jandejongh/pa3gyf-gpsdocxo/doc/dcim/2016-12-09 10.36.47-1.jpg

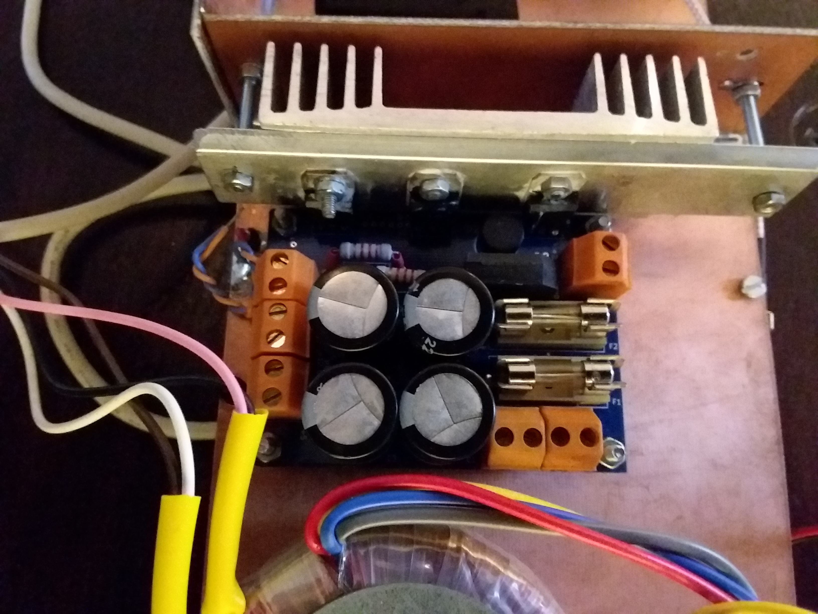
doc/dcim/2016-12-09 10.36.47-1.jpg
