jandejongh/pa3gyf-gpsdocxo/doc/dcim/2016-12-09 10.37.08.jpg

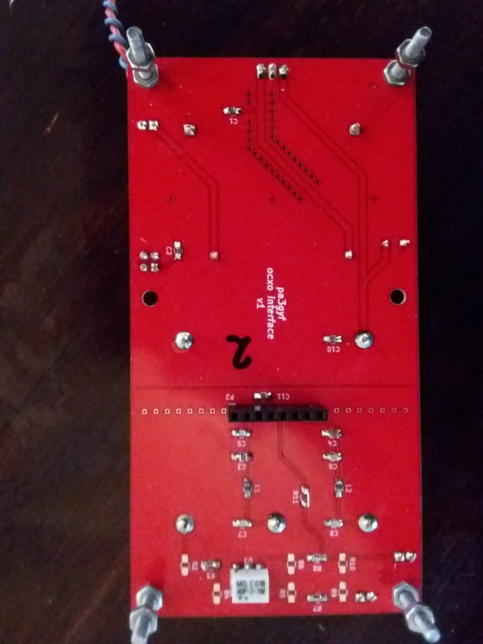
doc/dcim/2016-12-09 10.37.08.jpg
