jandejongh/pa3gyf-gpsdocxo/doc/dcim/2019-09-18 21.45.28.jpg

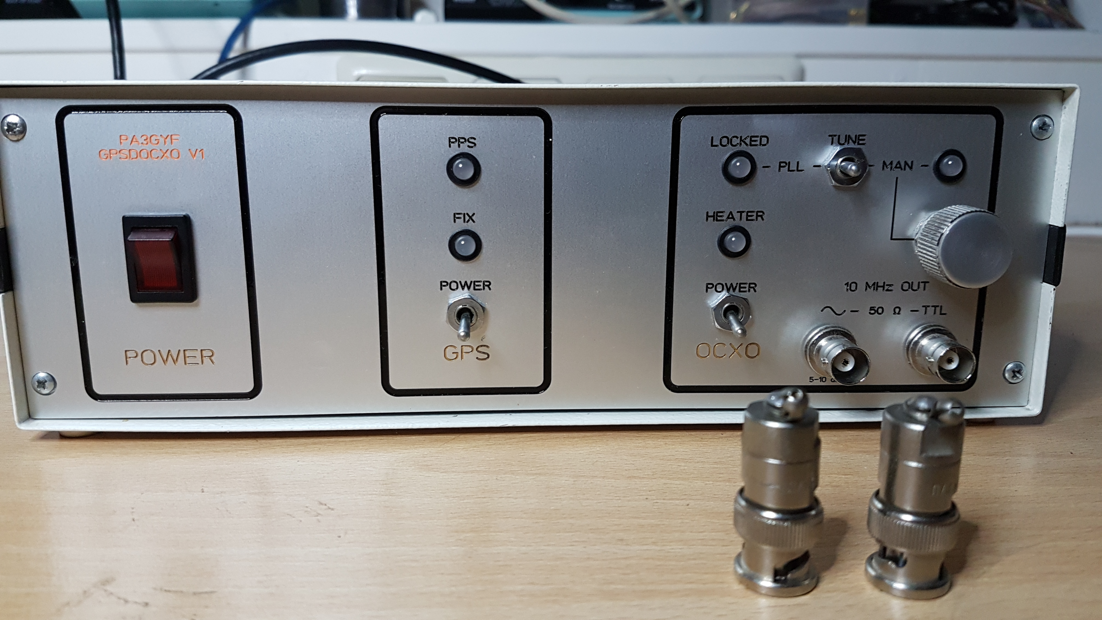
doc/dcim/2019-09-18 21.45.28.jpg
