jandejongh/pa3gyf-gpsdocxo/doc/dcim/2019-09-25 22.53.45.jpg

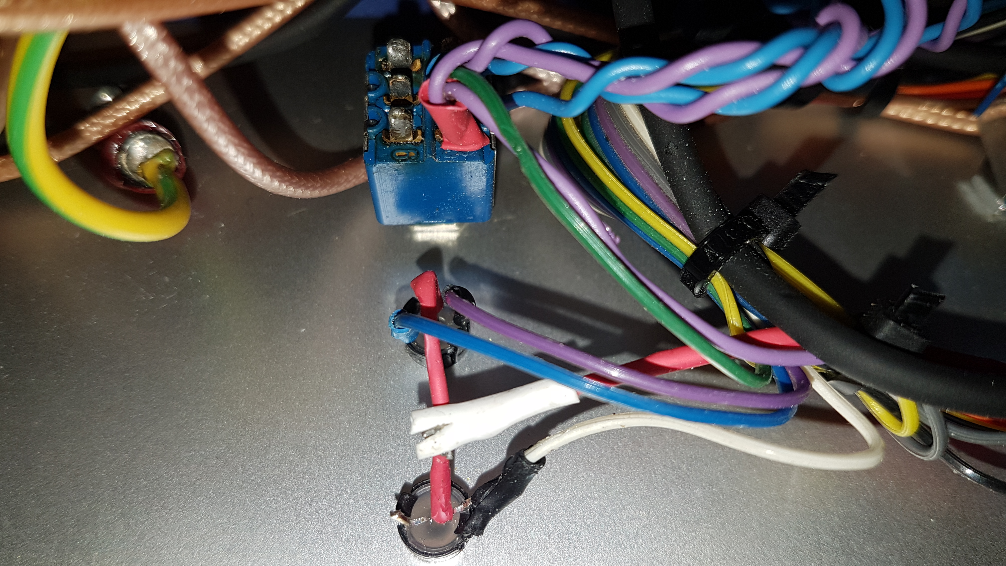
doc/dcim/2019-09-25 22.53.45.jpg
