jandejongh/pa3gyf-gpsdocxo/doc/dcim/2019-09-27 19.51.00.jpg

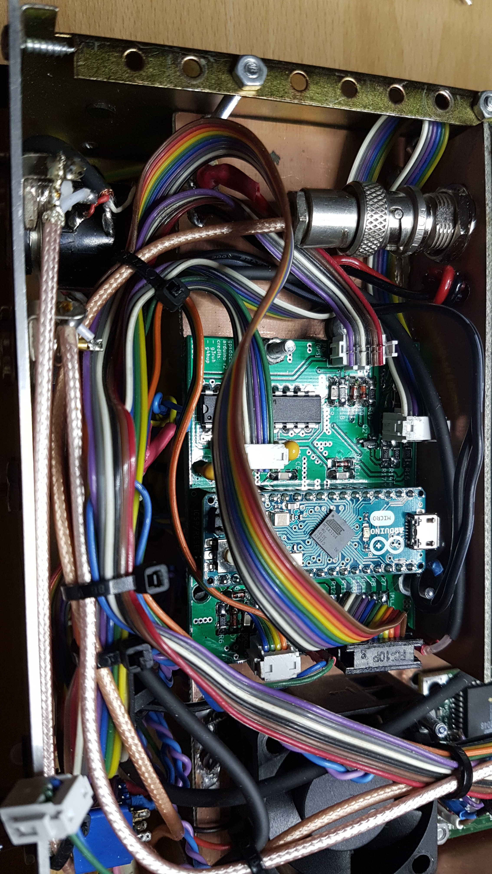
doc/dcim/2019-09-27 19.51.00.jpg
