jandejongh/pa3gyf-gpsdocxo/doc/dcim/2019-09-27 19.57.57.jpg

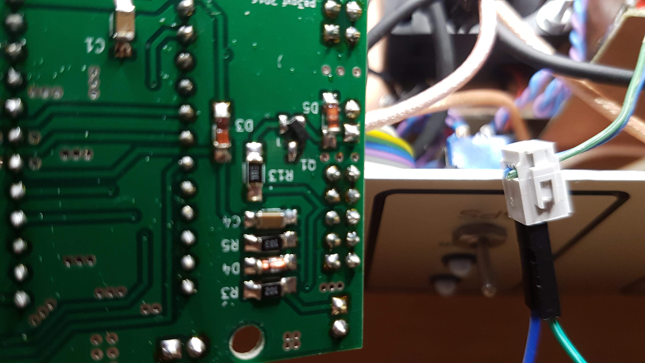
doc/dcim/2019-09-27 19.57.57.jpg
