jandejongh/pa3gyf-gpsdocxo/doc/dcim/2019-09-27 19.58.03.jpg

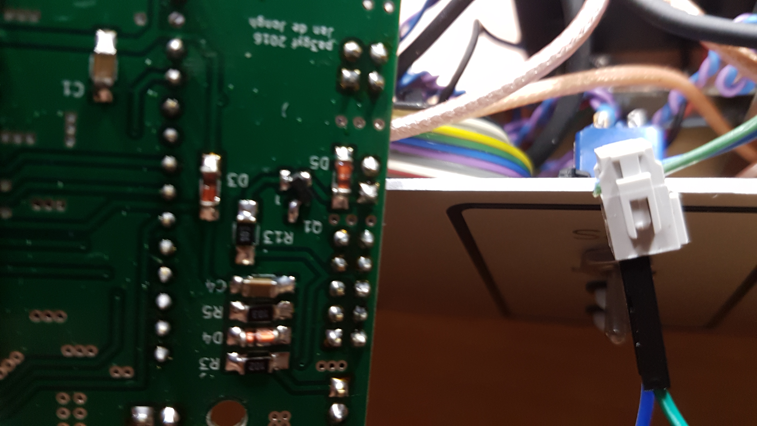
doc/dcim/2019-09-27 19.58.03.jpg
