jandejongh/pa3gyf-gpsdocxo/doc/dcim/2019-09-27 20.20.26.jpg

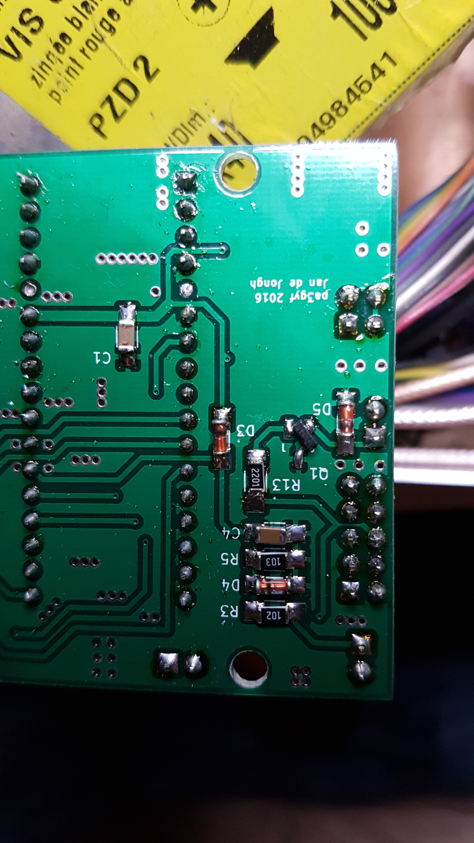
doc/dcim/2019-09-27 20.20.26.jpg
