jandejongh/pa3gyf-gpsdocxo/doc/dcim/2019-09-27 20.31.58.jpg

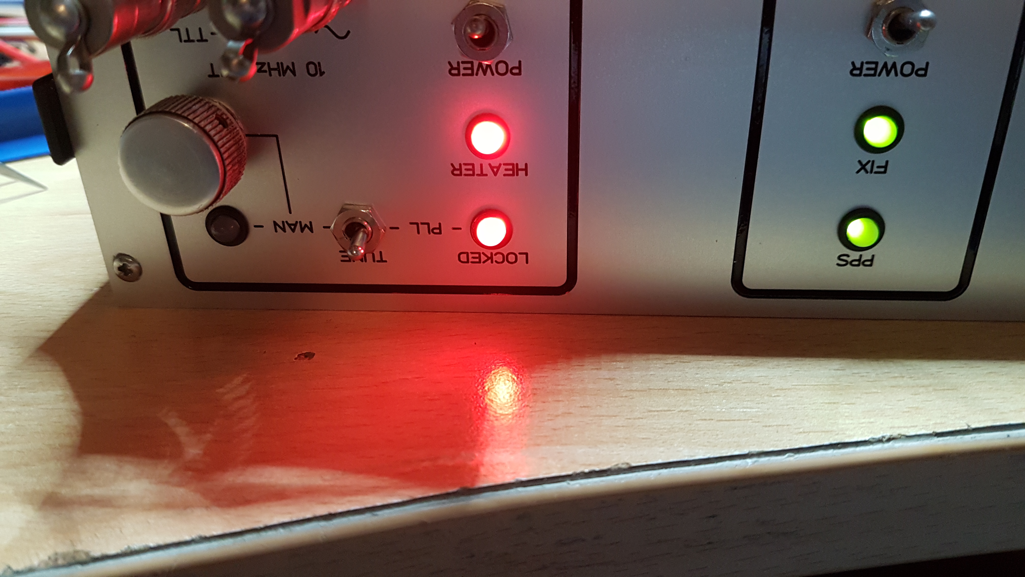
doc/dcim/2019-09-27 20.31.58.jpg
