jandejongh/pa3gyf-gpsdocxo/doc/dcim/2019-09-27 20.32.11.jpg

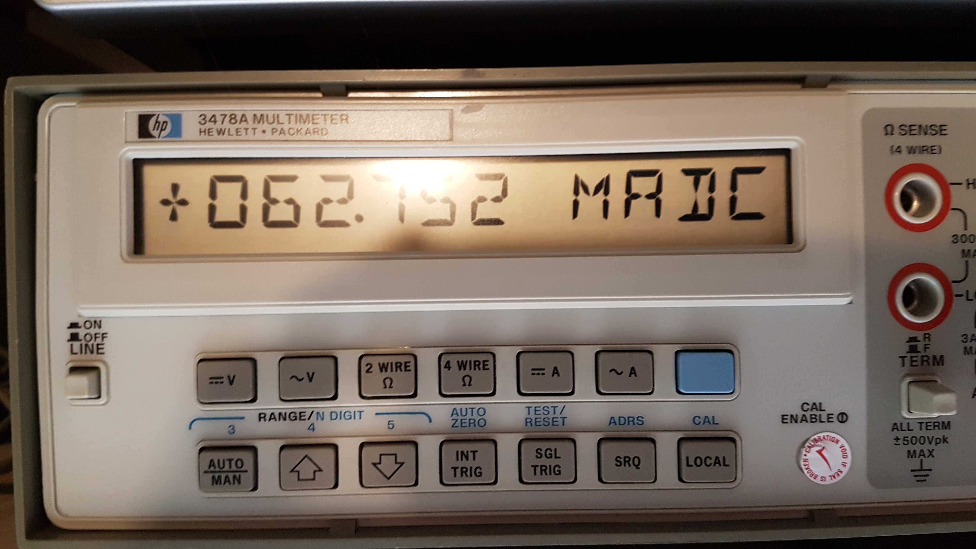
doc/dcim/2019-09-27 20.32.11.jpg
