jandejongh/pa3gyf-gpsdocxo/doc/dcim/2019-09-27 23.12.28.jpg

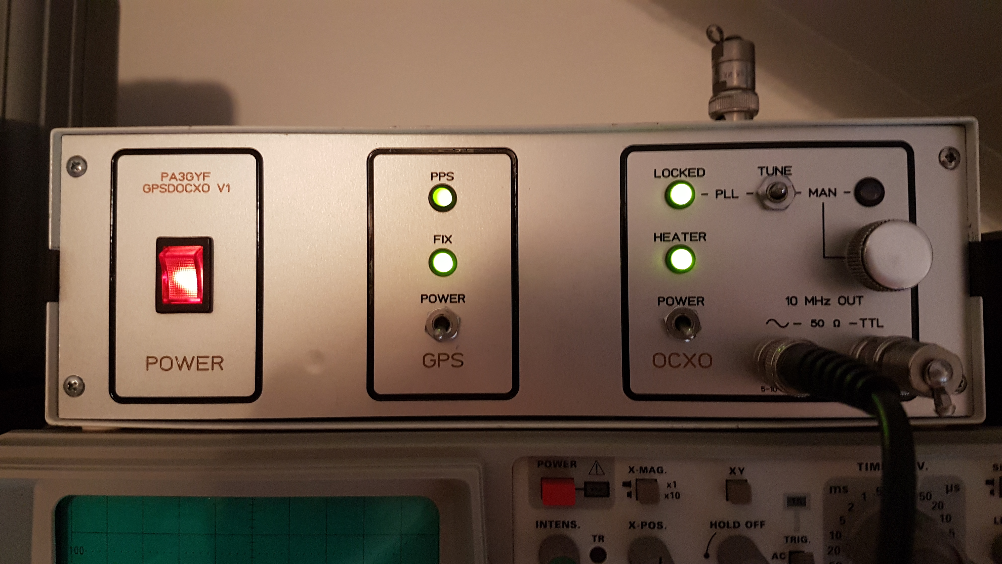
doc/dcim/2019-09-27 23.12.28.jpg
