jandejongh/pa3gyf-gpsdocxo/doc/dcim/2019-10-17 22.49.05.jpg

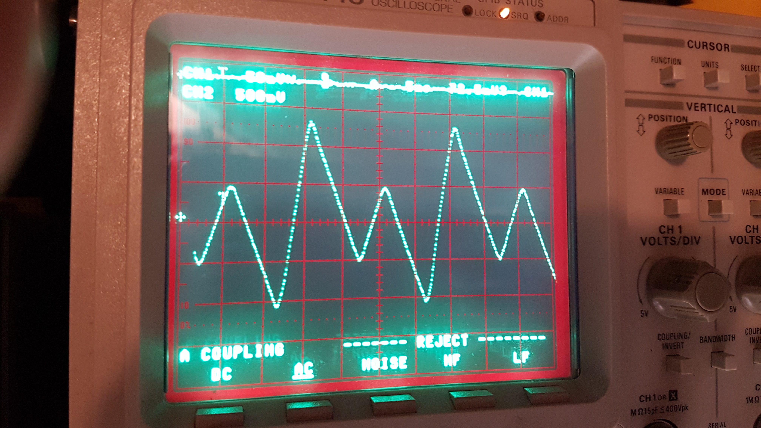
doc/dcim/2019-10-17 22.49.05.jpg
