jandejongh/pa3gyf-gpsdocxo/doc/dcim/2019-10-21 21.03.08.jpg

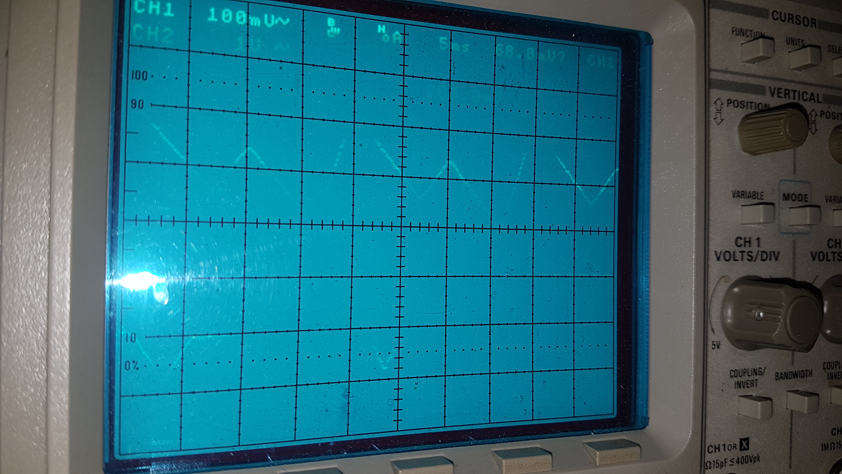
doc/dcim/2019-10-21 21.03.08.jpg
