jandejongh/pa3gyf-gpsdocxo/doc/dcim/2019-10-21 22.09.00.jpg

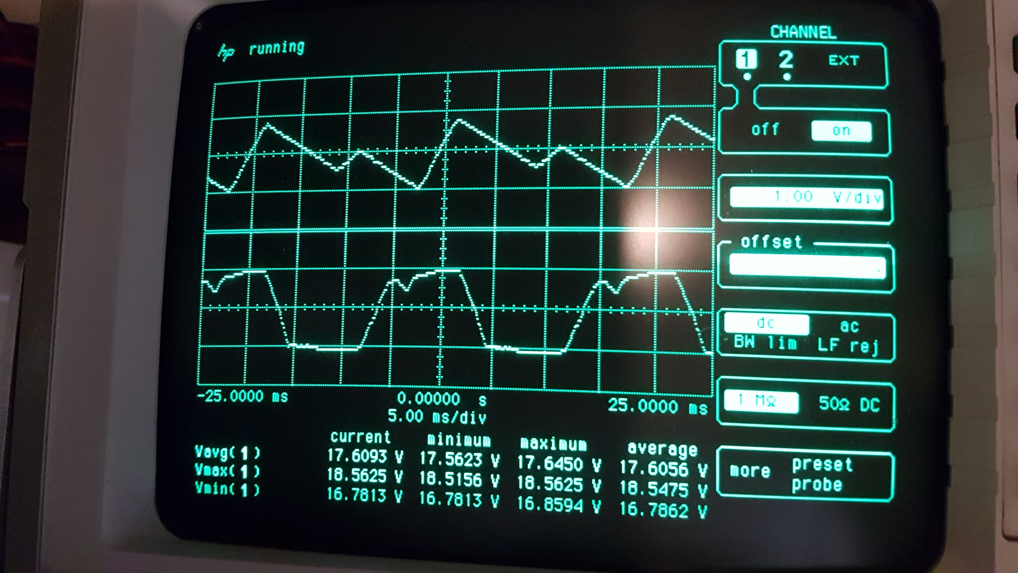
doc/dcim/2019-10-21 22.09.00.jpg
