jandejongh/pa3gyf-gpsdocxo/doc/pa3gyf-gpsdocxo-2016-v1-wiring-diagram.png

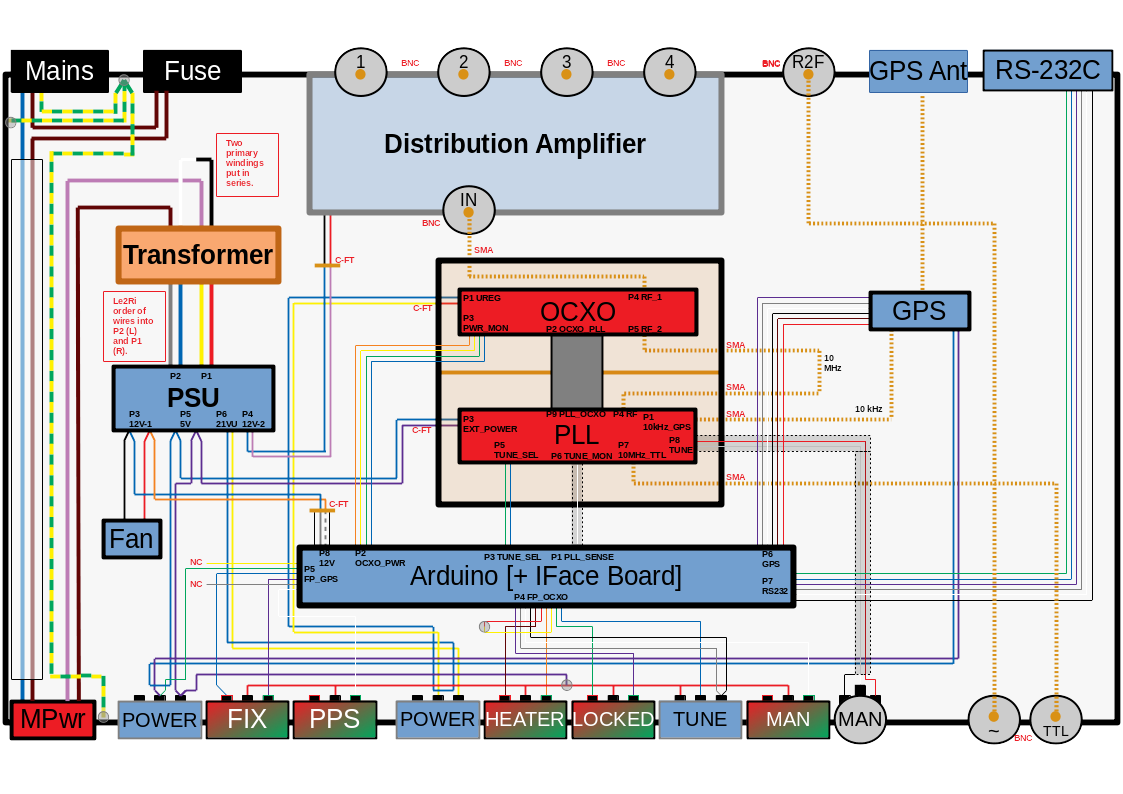
doc/pa3gyf-gpsdocxo-2016-v1-wiring-diagram.png
