jandejongh/pa3gyf-gpsdocxo/pcb/v1-kicad3/arduino/r2/pdf/pa3gyf-gpsdocxo-arduino-r2-F_SilkS.pdf

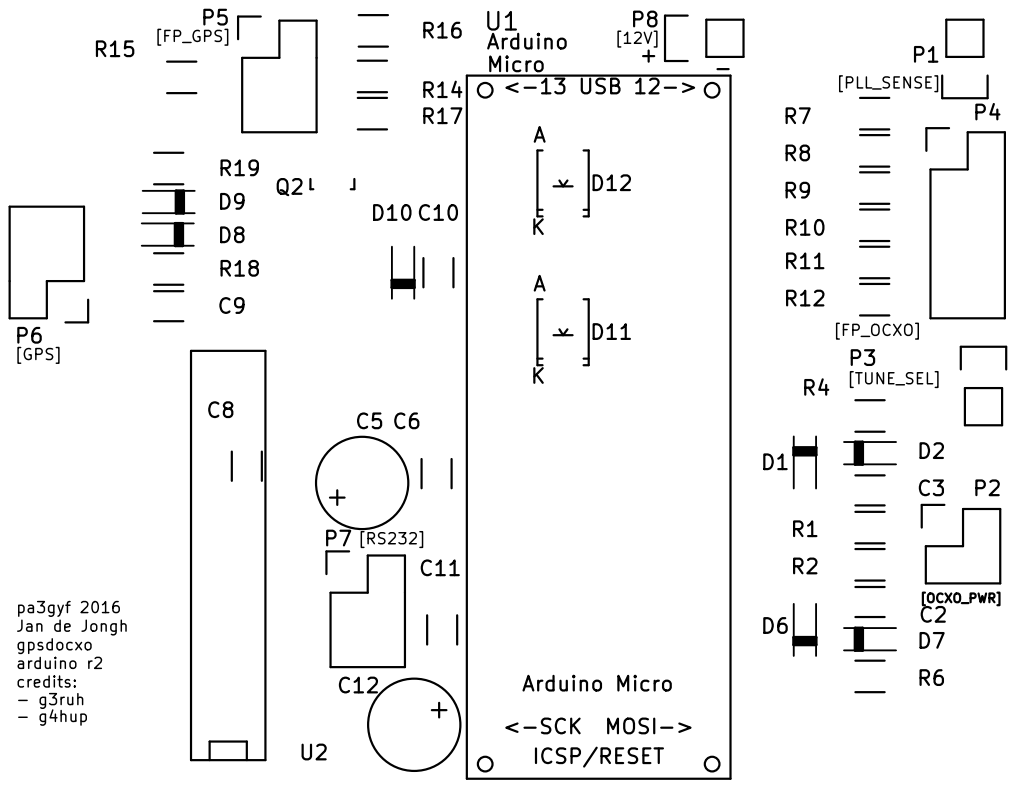
[picture p88: page 1]

<-13 USB 12-> Arduino Micro Arduino Micro
