jandejongh/pa3gyf-gpsdocxo/pcb/v1-kicad3/ocxo/r1/pdf/pa3gyf-gpsdocxo-ocxo.pdf

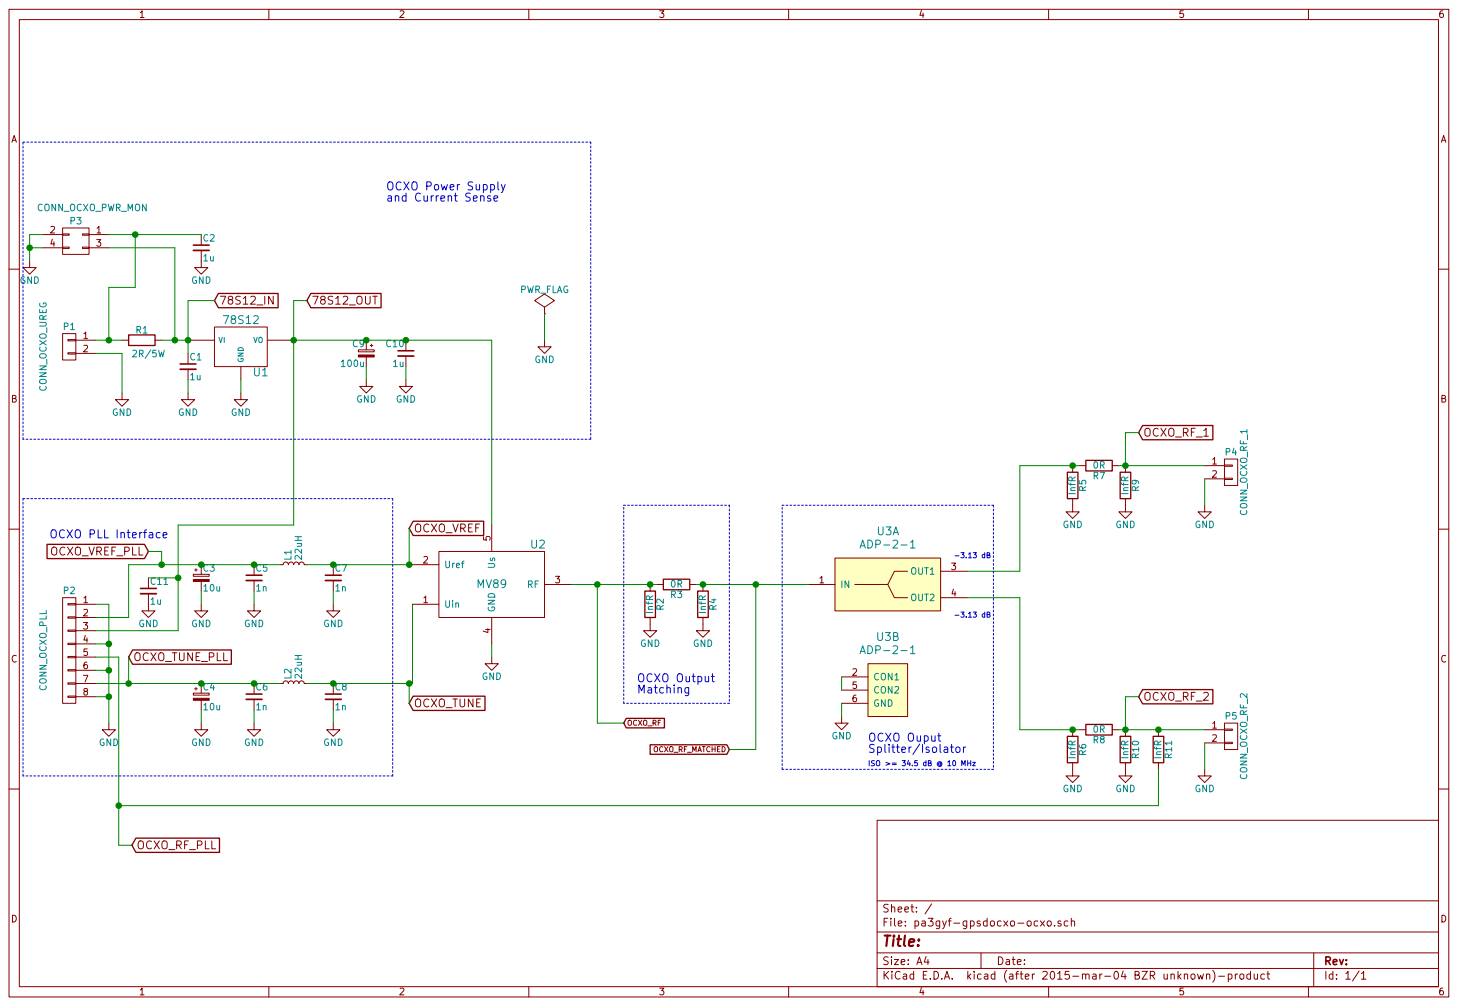
[picture p89: page 1]

GND OCXO Power Supply
and Current Sense

ADP-2-1 GND OCXO Output
