jandejongh/pa3gyf-gpsdocxo/pcb/v1-kicad3/pll/r2/pdf/pa3gyf-gpsdocxo-pll-B_SilkS.pdf

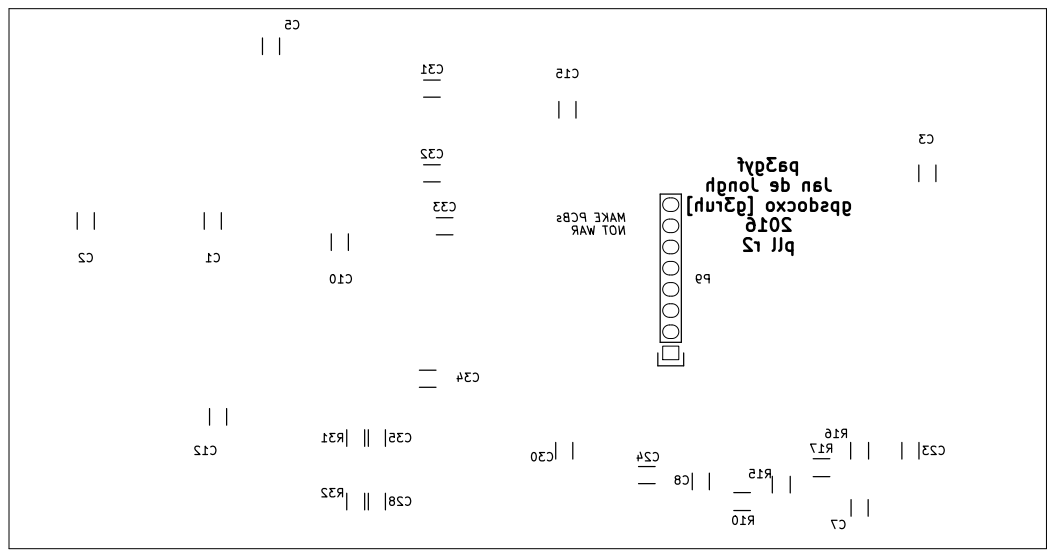
[picture p90: page 1]

MAKE PCBs NOT WAR pa3gyf
