jandejongh/pa3gyf-gpsdocxo/pcb/v1-kicad3/arduino/r2/pdf/pa3gyf-gpsdocxo-arduino-r2-F_Cu.pdf

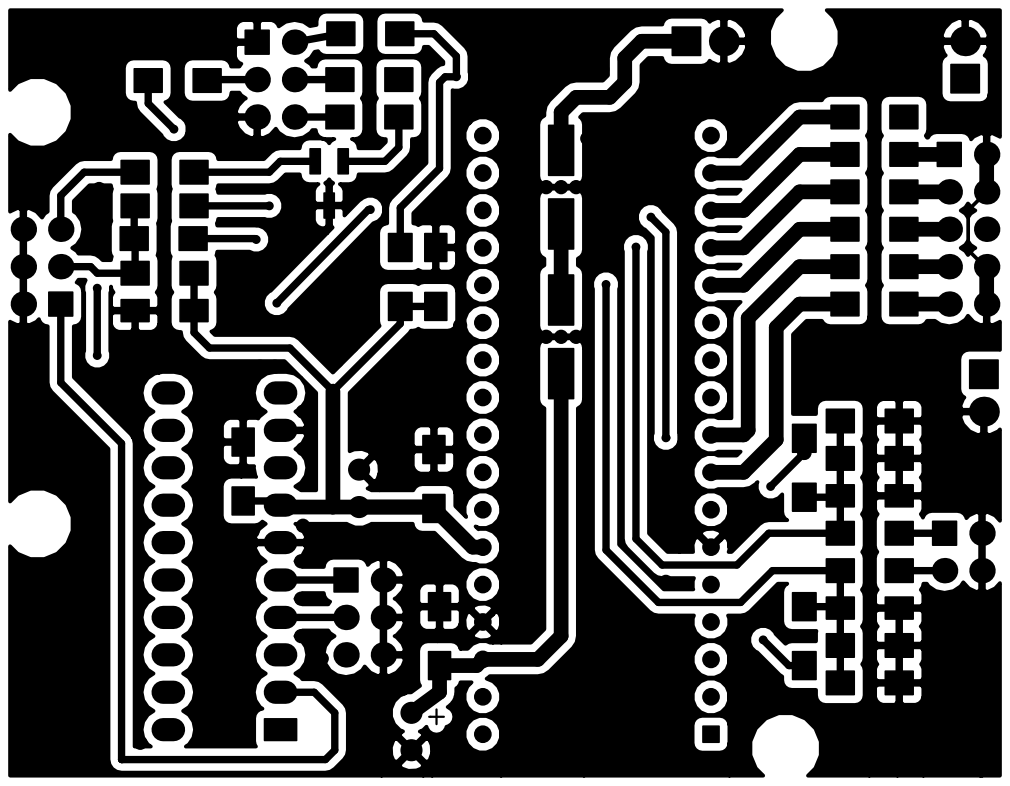
[picture p99: page 1]
