jandejongh/pa3gyf-gpsdocxo/pcb/v1-kicad3/arduino/r2/pdf/pa3gyf-gpsdocxo-arduino-r2-F_Mask.pdf

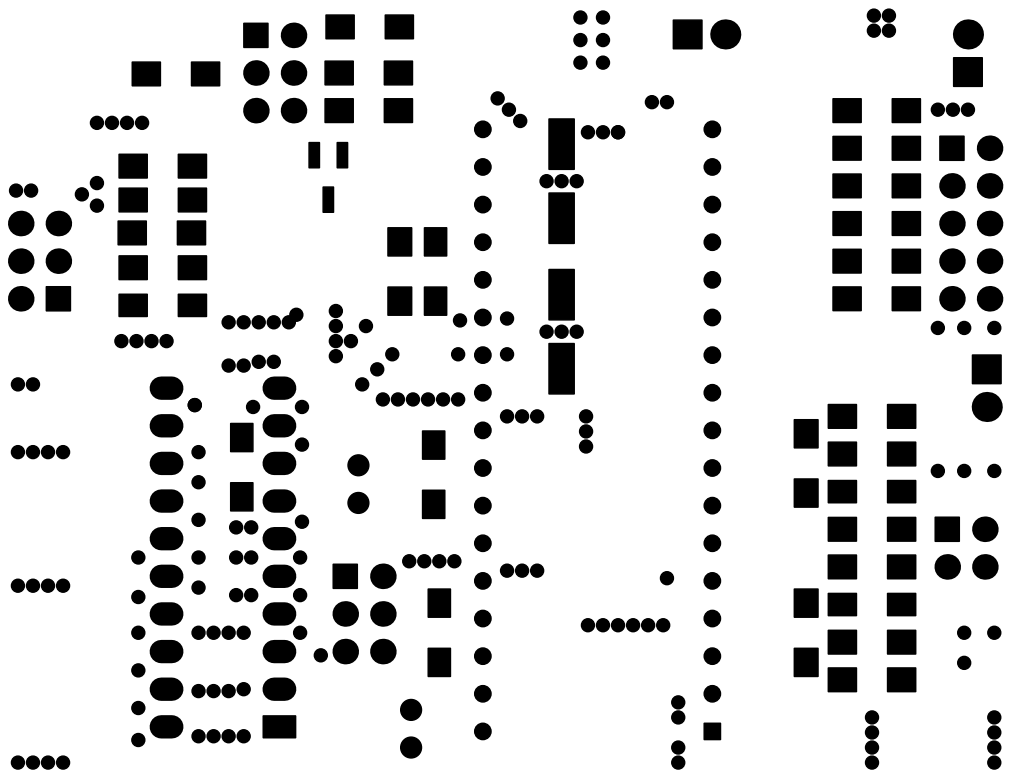
[picture p100: page 1]
