jandejongh/pa3gyf-gpsdocxo/pcb/v1-kicad3/ocxo/r1/pdf/pa3gyf-gpsdocxo-ocxo-B_Cu.pdf

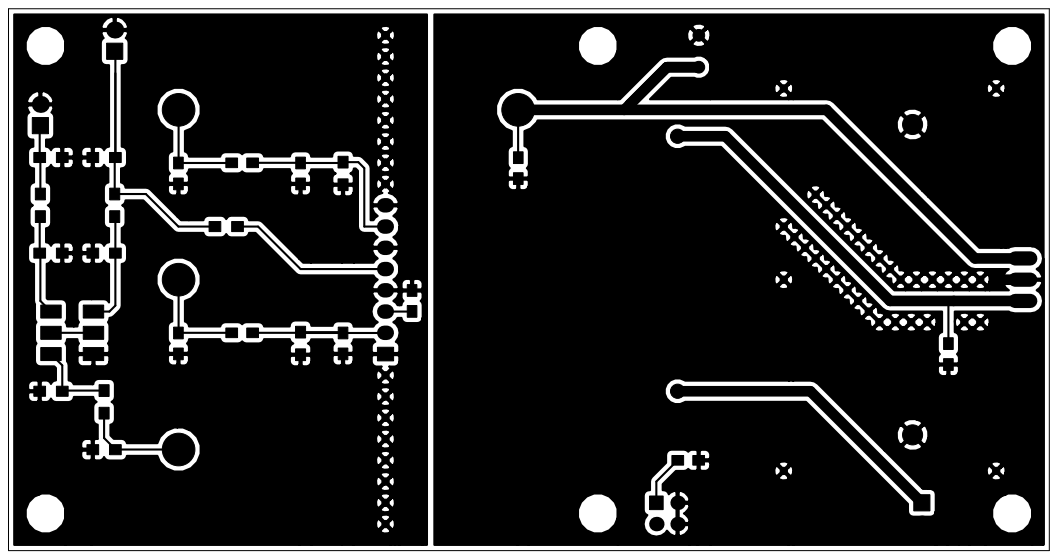
[picture p101: page 1]
