jandejongh/pa3gyf-gpsdocxo/pcb/v1-kicad3/ocxo/r1/pdf/pa3gyf-gpsdocxo-ocxo-B_SilkS.pdf

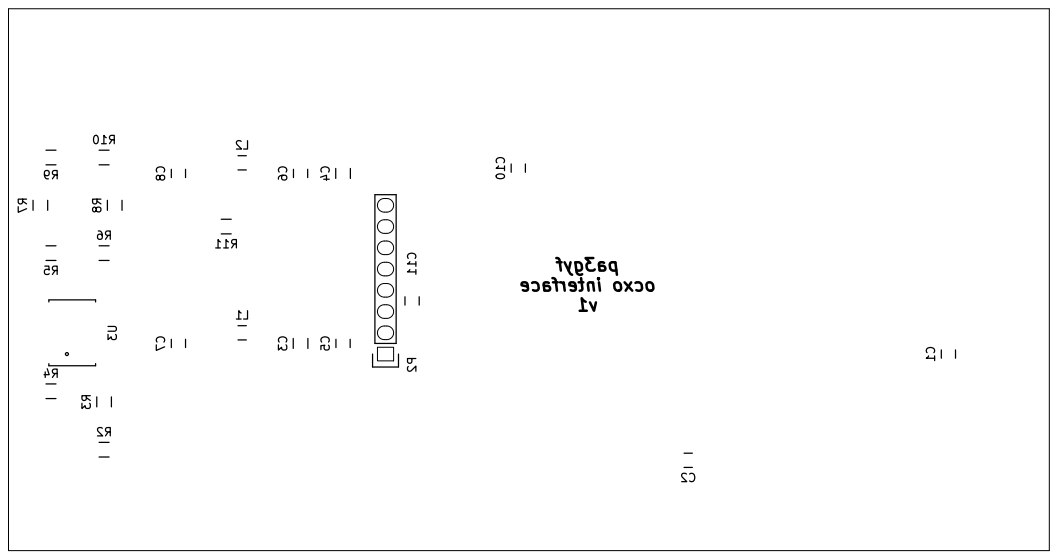
[picture p102: page 1]
