jandejongh/pa3gyf-gpsdocxo/pcb/v1-kicad3/ocxo/r1/pdf/pa3gyf-gpsdocxo-ocxo-F_Cu.pdf

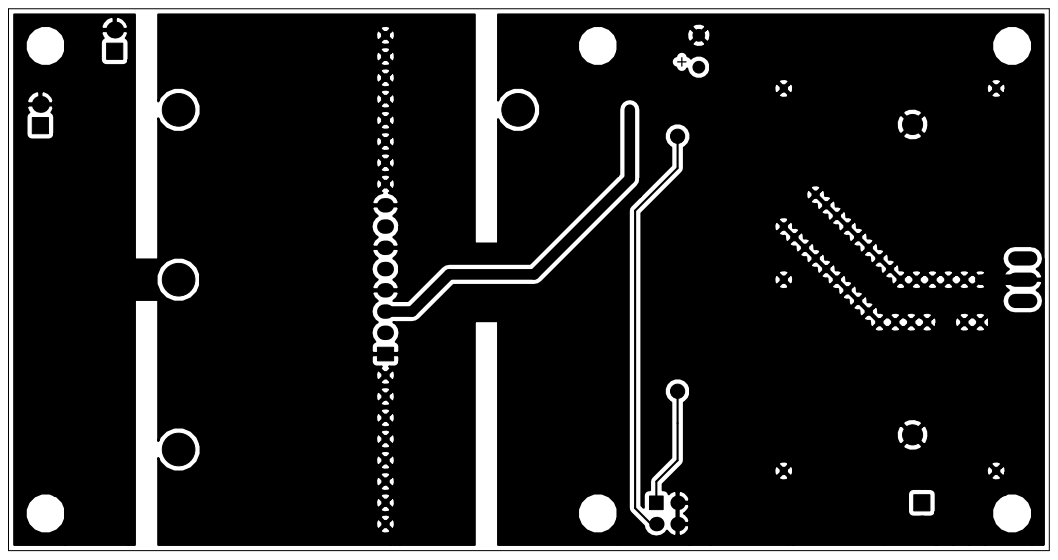
[picture p103: page 1]
