jandejongh/pa3gyf-gpsdocxo/pcb/v1-kicad3/ocxo/r1/pdf/pa3gyf-gpsdocxo-ocxo-F_SilkS.pdf

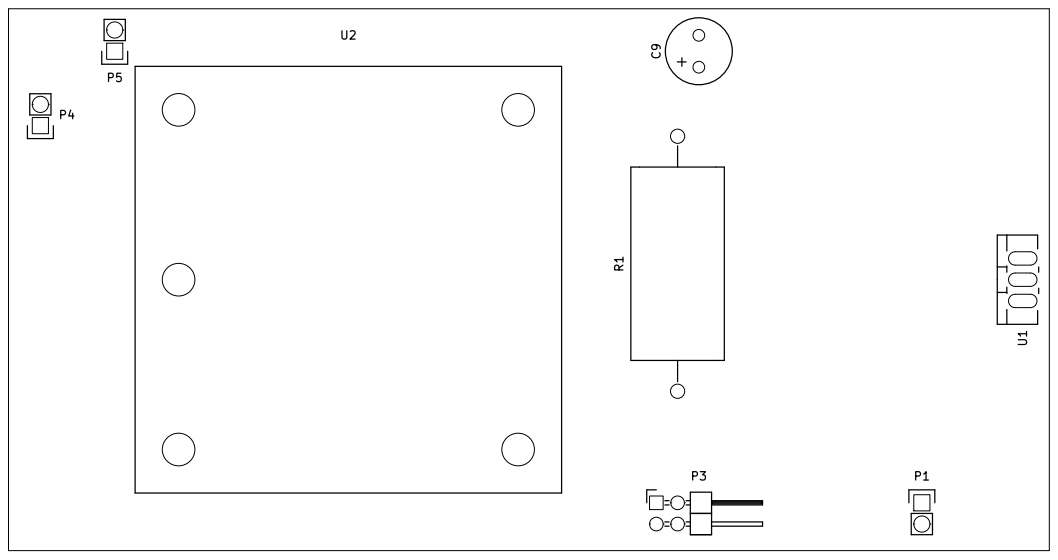
[picture p104: page 1]
