jandejongh/pa3gyf-gpsdocxo/pcb/v1-kicad3/pll/r2/pdf/pa3gyf-gpsdocxo-pll-B_Cu.pdf

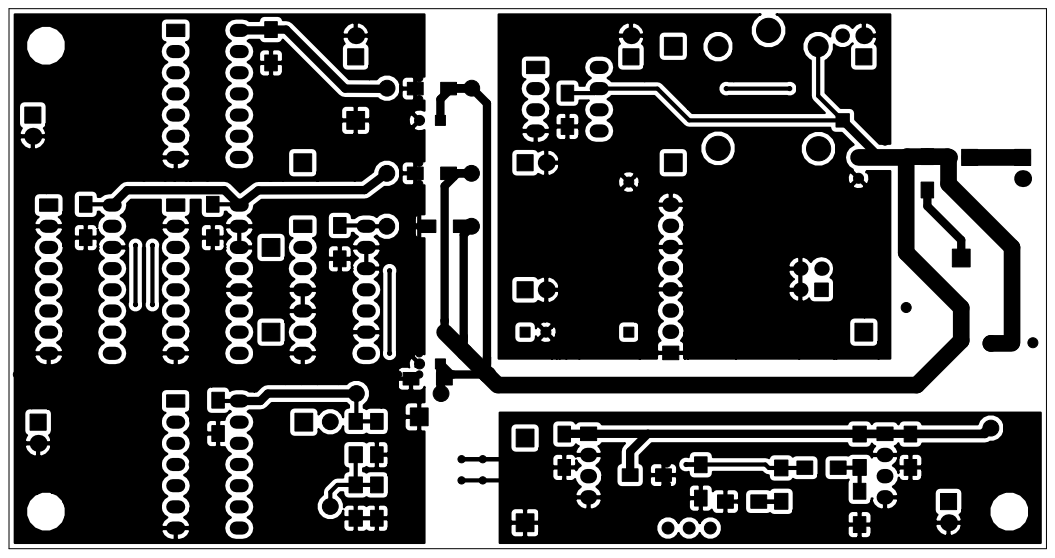
[picture p105: page 1]
