jandejongh/pa3gyf-gpsdocxo/pcb/v1-kicad3/pll/r2/pdf/pa3gyf-gpsdocxo-pll-B_Mask.pdf

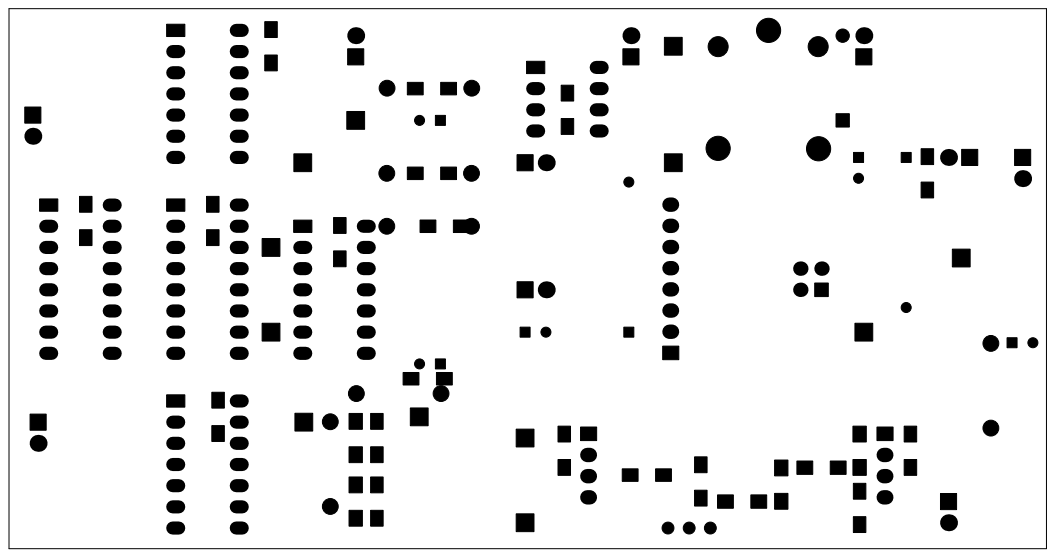
[picture p106: page 1]
