jandejongh/pa3gyf-gpsdocxo/pcb/v1-kicad3/pll/r2/pdf/pa3gyf-gpsdocxo-pll-F_Cu.pdf

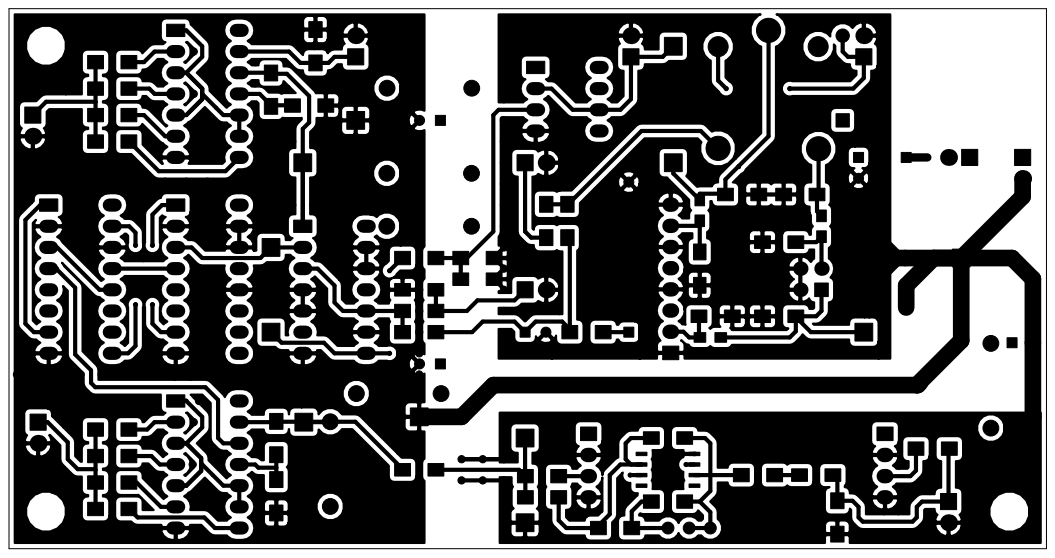
[picture p107: page 1]
