jandejongh/pa3gyf-gpsdocxo/pcb/v1-kicad3/pll/r2/pdf/pa3gyf-gpsdocxo-pll-F_Mask.pdf

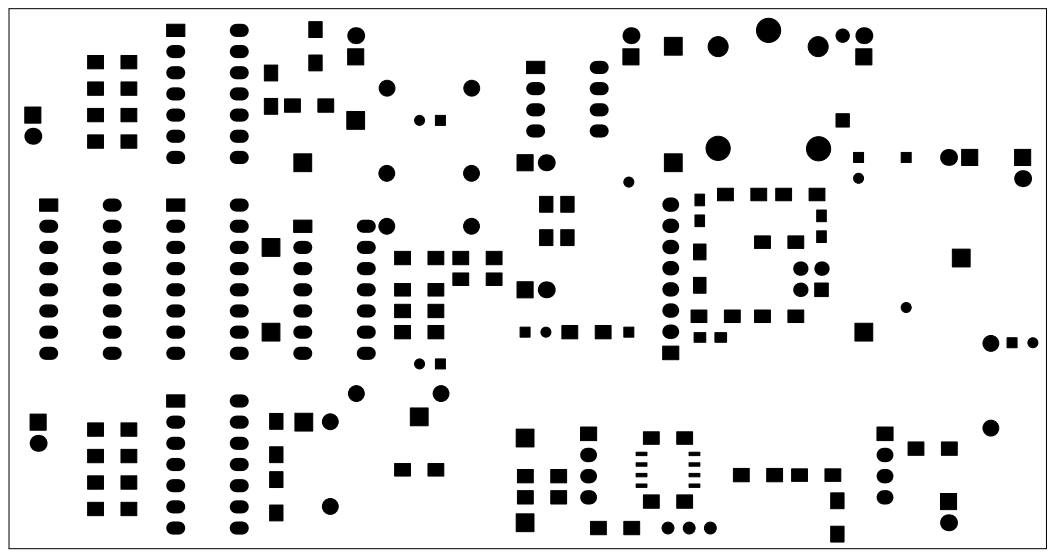
[picture p108: page 1]
