jandejongh/pa3gyf-gpsdocxo/pcb/v1-kicad3/pll/r2/pdf/pa3gyf-gpsdocxo-pll-F_SilkS.pdf

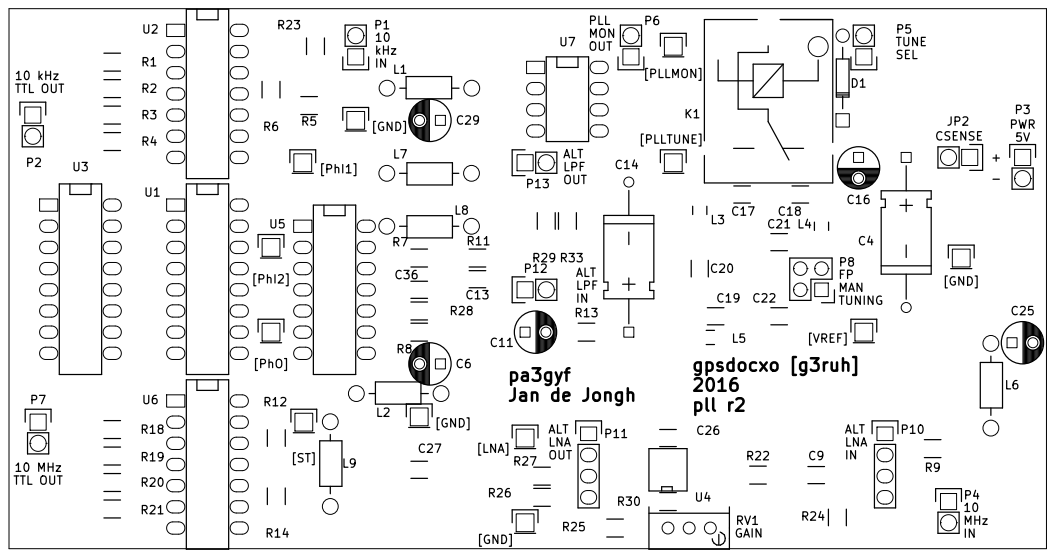
[picture p109: page 1]

SEL PLL MON OUT
